thesunRider/ESP32-visual-assistant/Docs/Images/dev.png

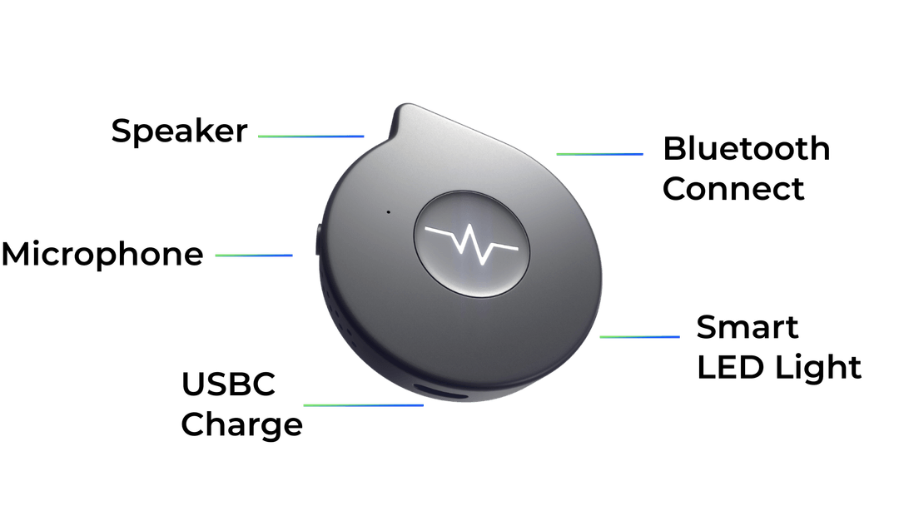
Docs/Images/dev.png
