thesunRider/ESP32-visual-assistant/Docs/Images/wareit.jpeg

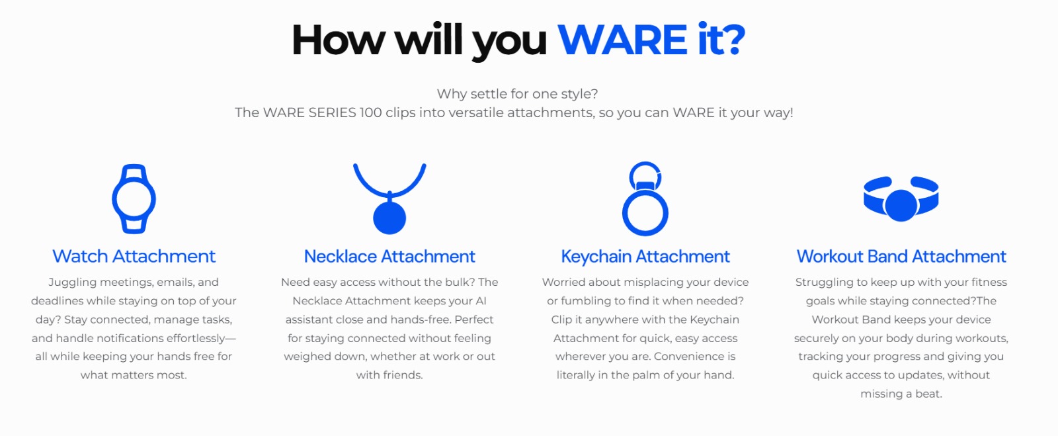
Docs/Images/wareit.jpeg
