thesunRider/ESP32-visual-assistant/Docs/Images/WhatsApp Image 2024-12-23 at 5.31.38 PM.jpeg

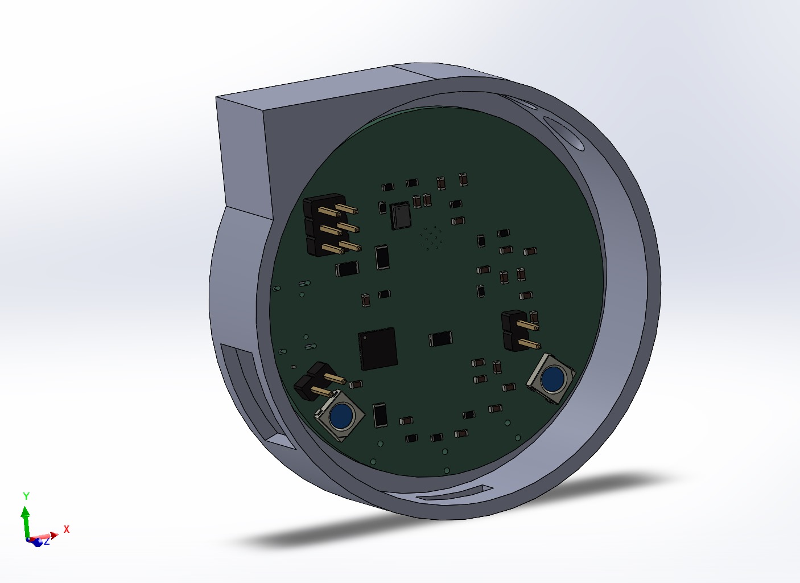
Docs/Images/WhatsApp Image 2024-12-23 at 5.31.38 PM.jpeg
