thesunRider/ESP32-visual-assistant/Docs/Images/WhatsApp Image 2024-12-23 at 6.42.17 PM.jpeg

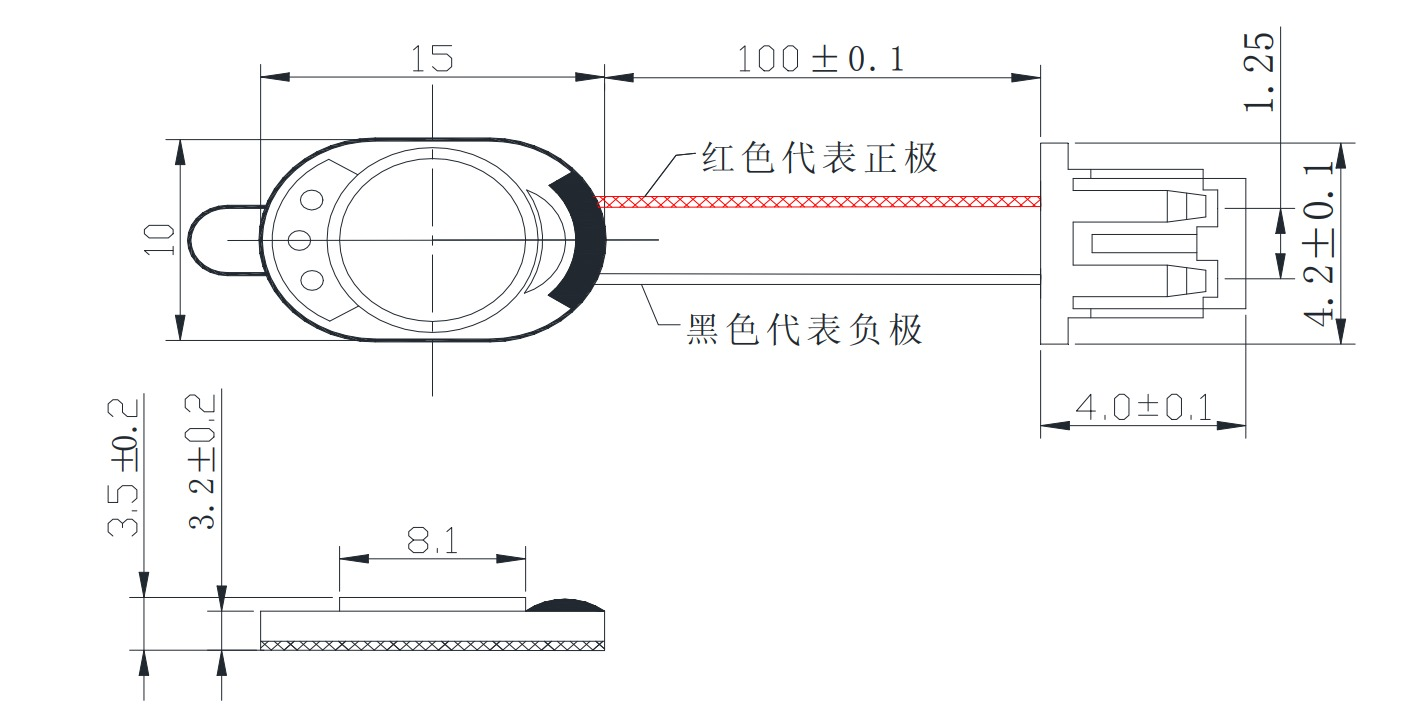
Docs/Images/WhatsApp Image 2024-12-23 at 6.42.17 PM.jpeg
