thesunRider/ESP32-visual-assistant/Docs/Reference Schematic/reference_esp32_amplifier_bff_pcb.jpeg

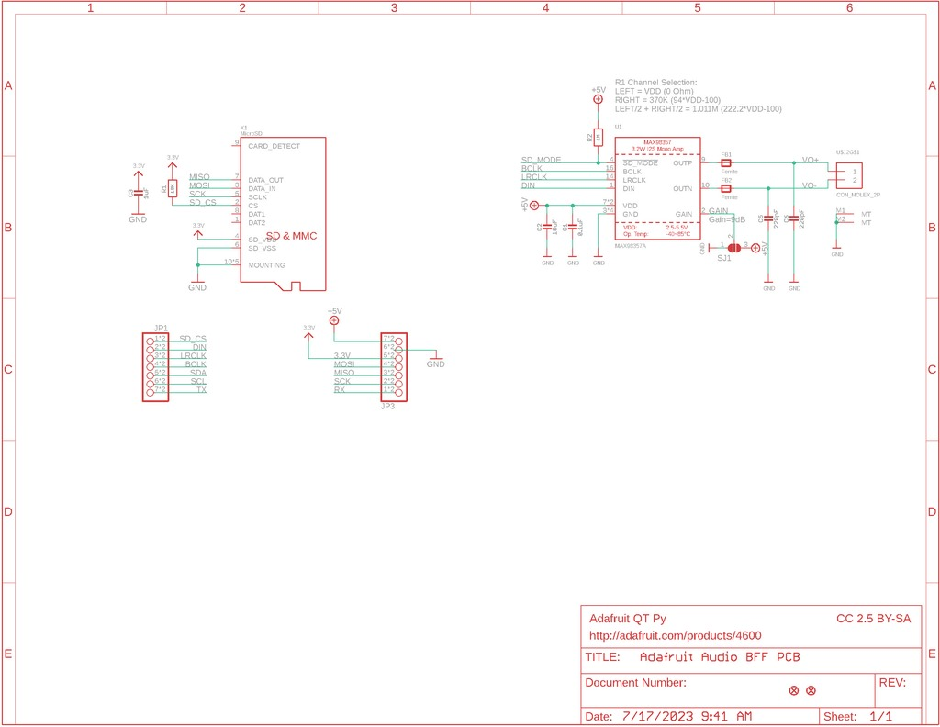
Docs/Reference Schematic/reference_esp32_amplifier_bff_pcb.jpeg
