thesunRider/ESP32-visual-assistant/fllor planning.png

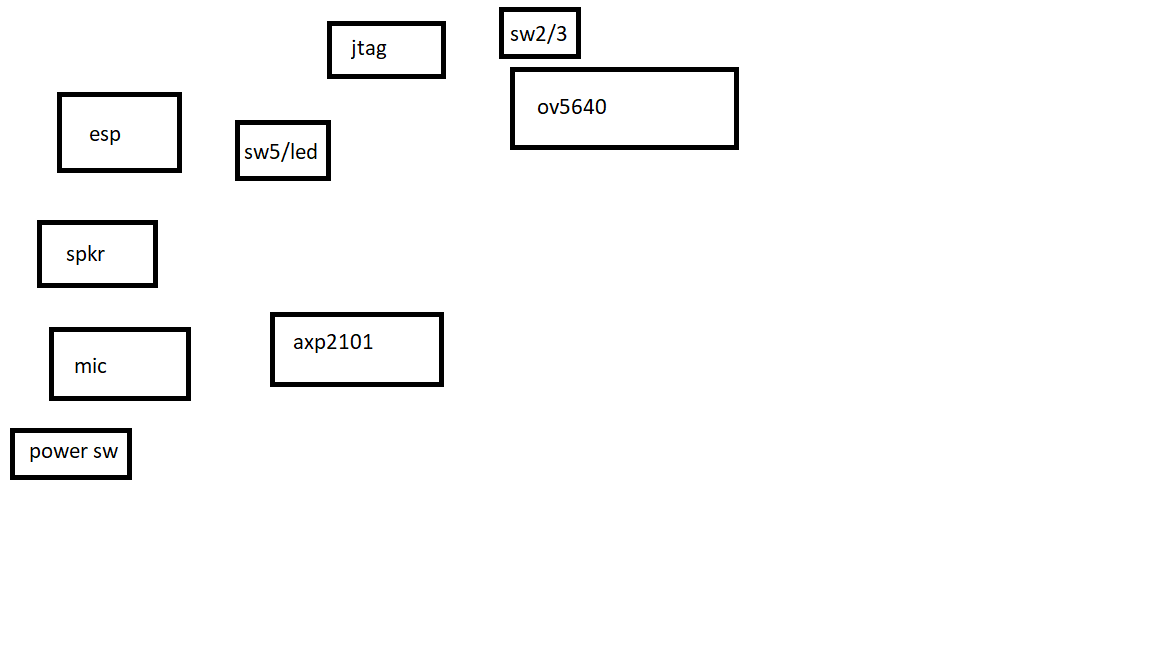
fllor planning.png
