thesunRider/ESP32-visual-assistant/images/case_2.jpg

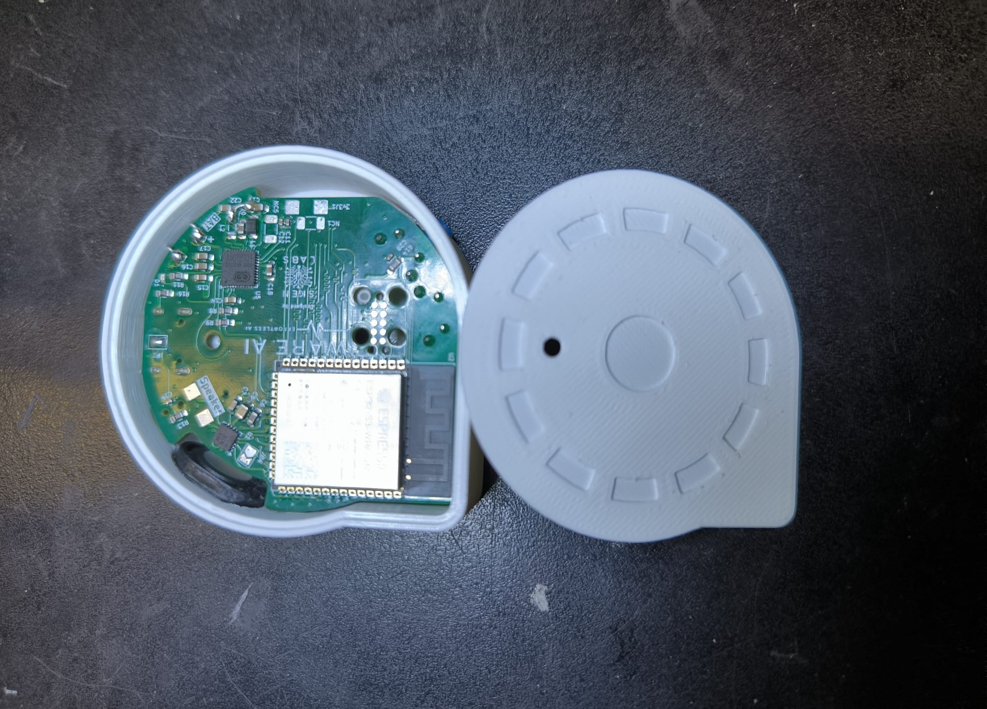
images/case_2.jpg
