thesunRider/ESP32-visual-assistant/images/case_3.jpg

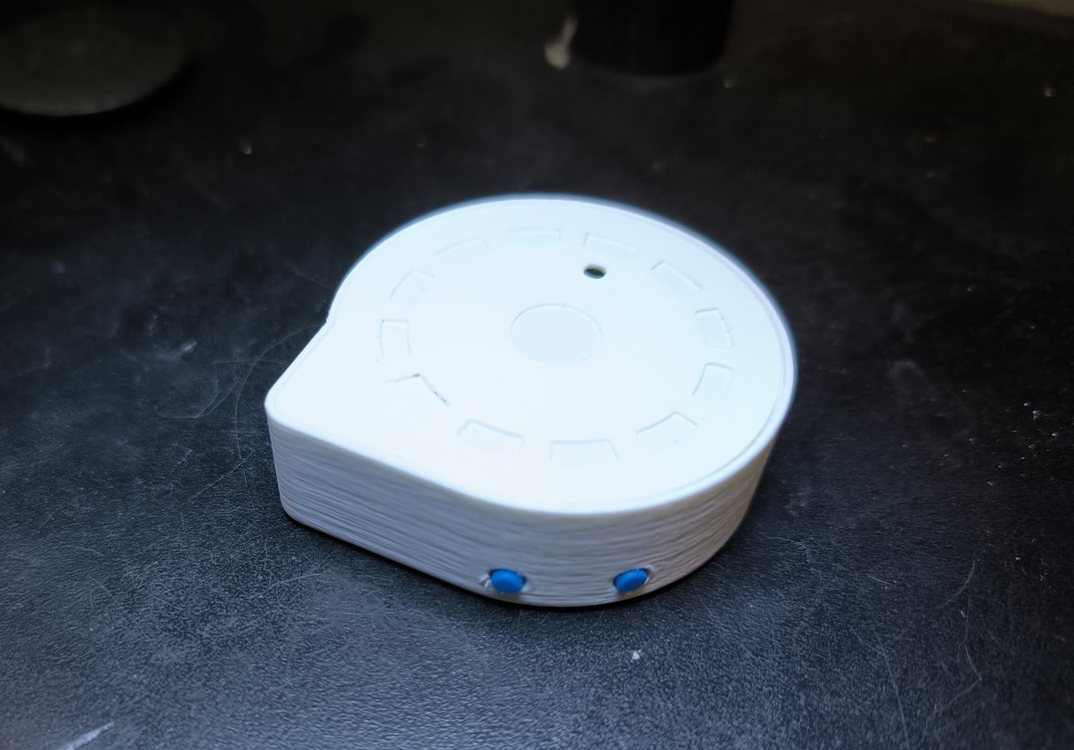
images/case_3.jpg
