thesunRider/ESP32-visual-assistant/images/Microscope_1.jpeg

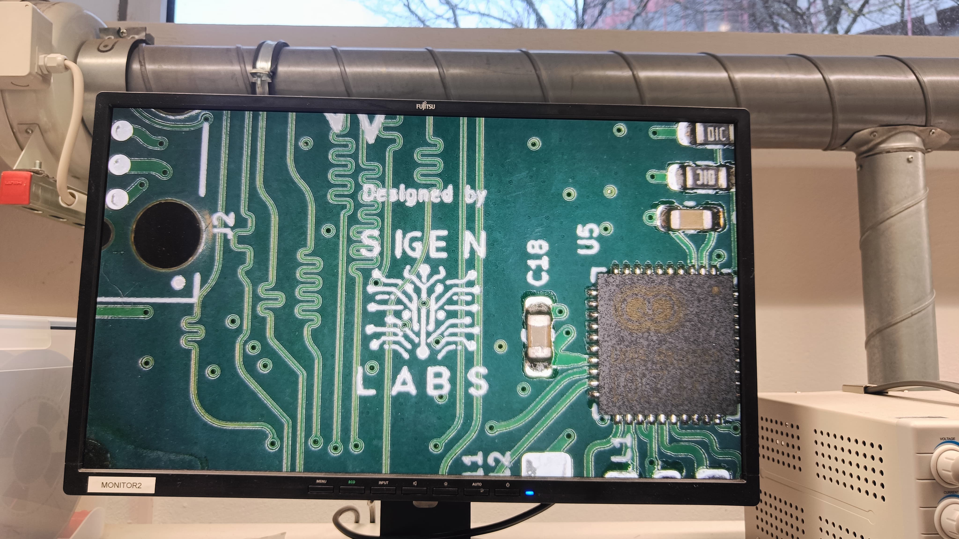
images/Microscope_1.jpeg
