thesunRider/ESP32-visual-assistant/images/PCB_2.jpeg

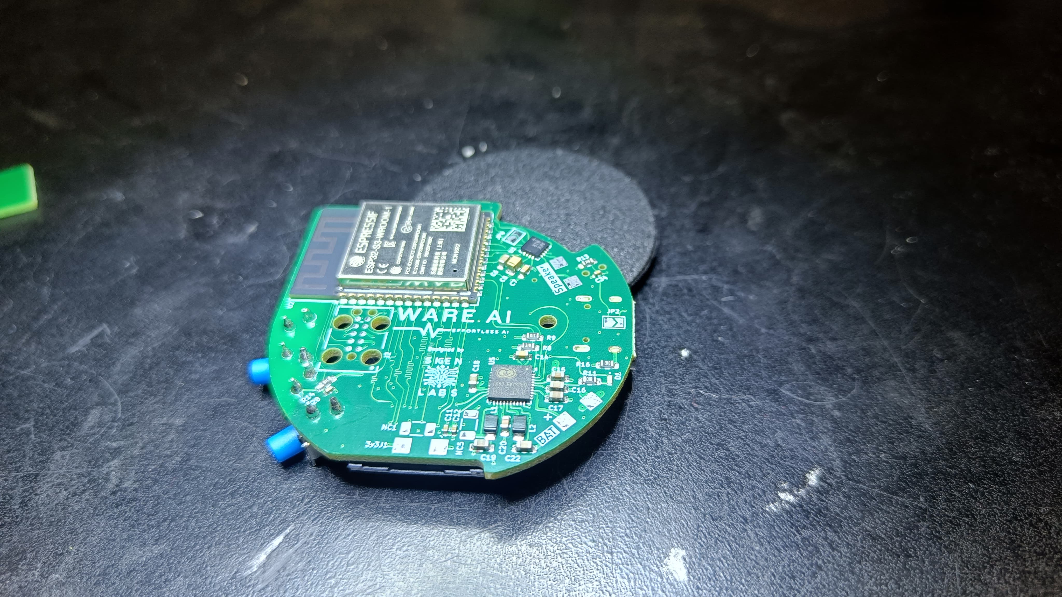
images/PCB_2.jpeg
