thesunRider/ESP32-visual-assistant/images/PCB_Bottom.jpg

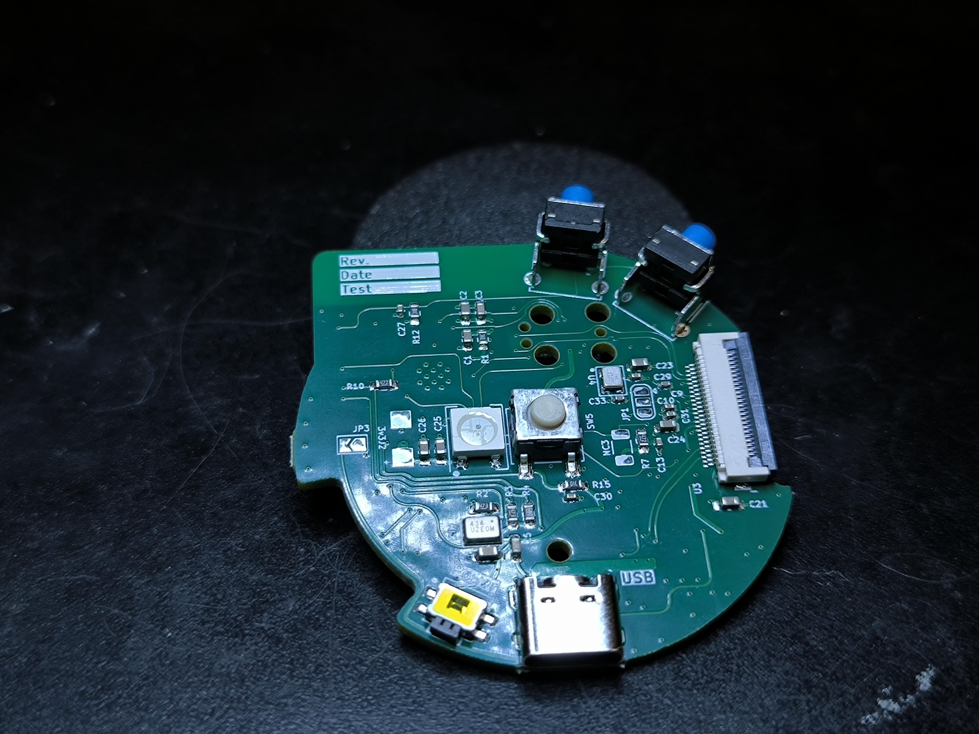
images/PCB_Bottom.jpg
