thesunRider/ESP32-visual-assistant/images/PCB_Top.jpg

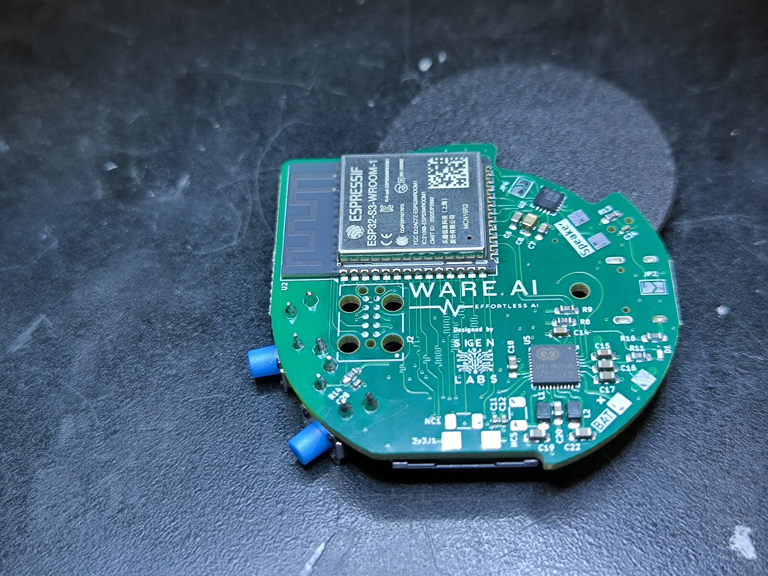
images/PCB_Top.jpg
