thesunRider/ESP32-visual-assistant/Programmer Connection.jpg

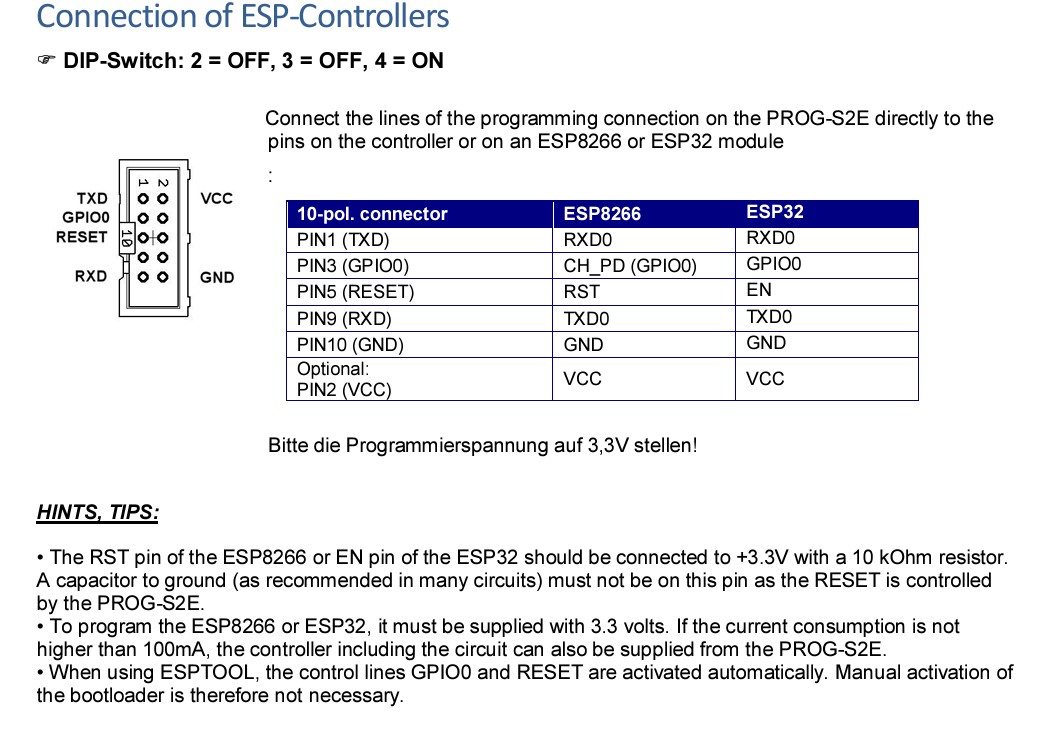
Programmer Connection.jpg
