thesunRider/ESP32-visual-assistant/Model/schematic_rev1.pdf

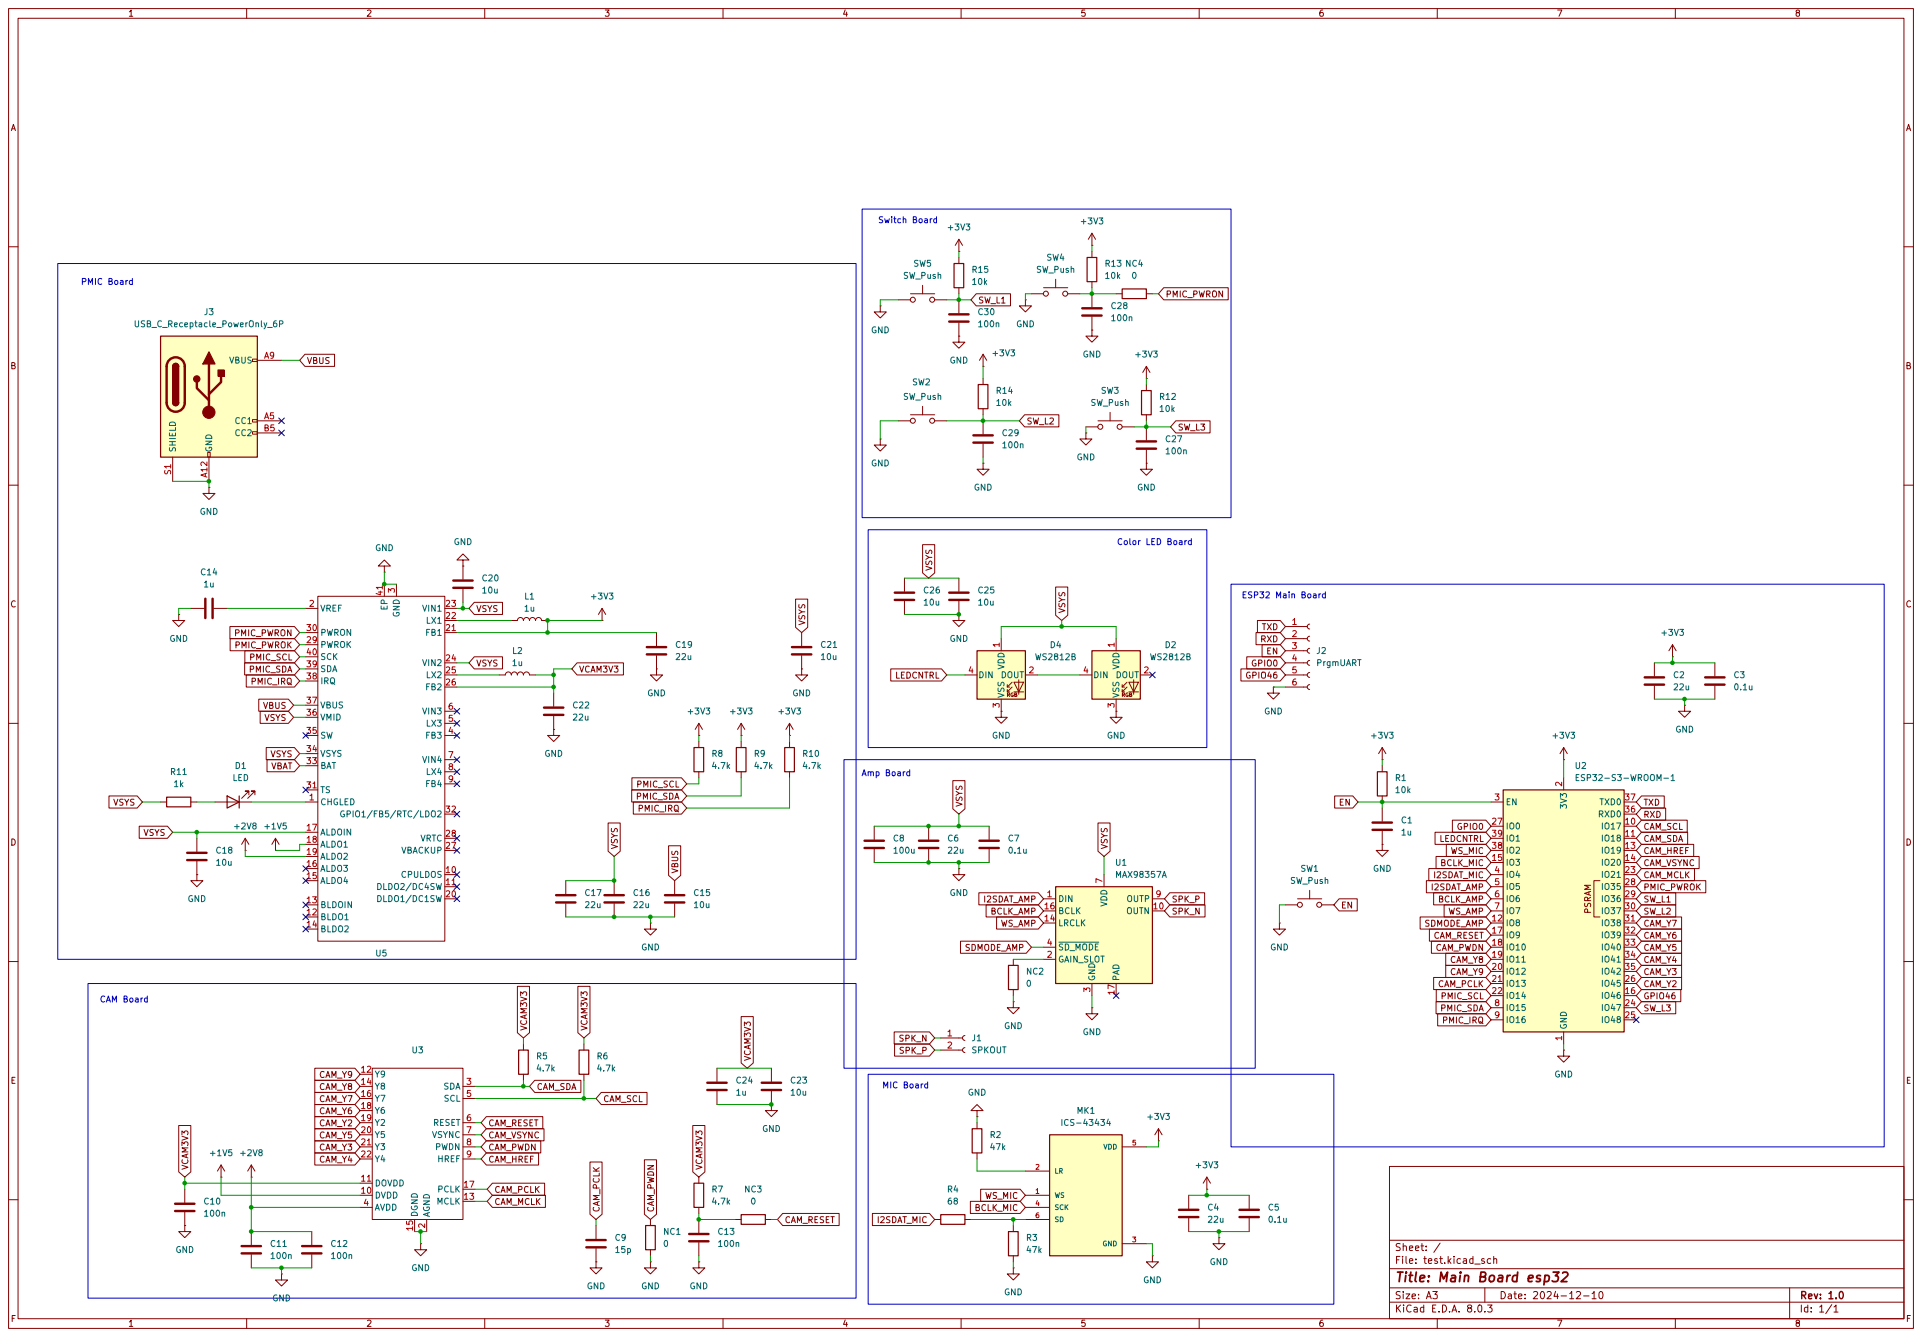
[picture p42: page 1]
