thesunRider/ESP32-visual-assistant/Extras/OV5640-Camera-Board-(A)-Code/OV5640_F746I-C (4.3 inch)/Src/main.c

/**
  ******************************************************************************
  * File Name          : main.c
  * Description        : Main program body
  ******************************************************************************
  ** This notice applies to any and all portions of this file
  * that are not between comment pairs USER CODE BEGIN and
  * USER CODE END. Other portions of this file, whether 
  * inserted by the user or by software development tools
  * are owned by their respective copyright owners.
  *
  * COPYRIGHT(c) 2017 STMicroelectronics
  *
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
  ******************************************************************************
  */

/* Includes ------------------------------------------------------------------*/
#include "main.h"
#include "stm32f7xx_hal.h"
#include "dcmi.h"
#include "dma.h"
#include "dma2d.h"
#include "ltdc.h"
#include "usart.h"
#include "gpio.h"
#include "fmc.h"

/* USER CODE BEGIN Includes */

#include "../BSP/stm32746g_sdram.h"
#include "../BSP/stm32746g_LCD.h"
#include "../BSP/ov5640.h"

/* USER CODE END Includes */


/* USER CODE BEGIN PV */

/* USER CODE END PV */

void SystemClock_Config(void);

/* USER CODE BEGIN PFP */

/* USER CODE END PFP */

int main(void)
{

  /* Enable I-Cache-------------------------------------------------------------*/
  SCB_EnableICache();

  /* Enable D-Cache-------------------------------------------------------------*/
  SCB_EnableDCache();

  /* MCU Configuration----------------------------------------------------------*/

  /* Reset of all peripherals, Initializes the Flash interface and the Systick. */
  HAL_Init();

  /* Configure the system clock */
  SystemClock_Config();

  /* Initialize all configured peripherals */
  MX_GPIO_Init();
  MX_DMA_Init();
  MX_DMA2D_Init();
  MX_FMC_Init();
  MX_LTDC_Init();
  MX_USART1_UART_Init();
  MX_DCMI_Init();

  /* USER CODE BEGIN 2 */
  
  
        BSP_SDRAM_Init();                   
        
	BSP_LCD_Init();
        BSP_LCD_SetLayerVisible(1, DISABLE);
        BSP_LCD_SelectLayer(0);
        BSP_LCD_DisplayOn();
     
        // turn ON the LCD backlight
        HAL_GPIO_WritePin(LCD_BACK_LIGHT_GPIO_Port,LCD_BACK_LIGHT_Pin,GPIO_PIN_SET);  
        BSP_LCD_Clear(LCD_COLOR_WHITE);
        BSP_LCD_SetBackColor(LCD_COLOR_WHITE);
        BSP_LCD_SetTextColor(LCD_COLOR_RED);
	BSP_LCD_SetFont(&Font20);    
        
        BSP_LCD_DisplayStringAt(0, 60, (uint8_t *)"Initializing, please wait ...", CENTER_MODE);
        printf("Initializing, please wait ...\r\n");
        
        while(OV5640_Init())
        {            
                printf("OV5640 error, please check !\r\n");
                BSP_LCD_Clear(LCD_COLOR_WHITE);
                HAL_Delay(200);
                BSP_LCD_DisplayStringAt(0, 60, (uint8_t *)"OV5640 error, please check !", CENTER_MODE);
                HAL_Delay(300);
        }              
        OV5640_RGB565_Mode();	
	OV5640_Light_Mode(0);	   //set auto
	OV5640_Color_Saturation(3); //default
	OV5640_Brightness(4);	//default
	OV5640_Contrast(3);     //default
	OV5640_Sharpness(33);	//set auto
        
        BSP_LCD_Clear(LCD_COLOR_WHITE);
        BSP_LCD_SetTextColor(LCD_COLOR_BLUE);  
        BSP_LCD_DisplayStringAt(0, 60, (uint8_t *)"Waveshare OV5640 Test", CENTER_MODE);
        BSP_LCD_DisplayStringAt(0, 130, (uint8_t *)" WAKE UP:   JPEG", LEFT_MODE);
        BSP_LCD_DisplayStringAt(0, 160, (uint8_t *)" JOYSTICK:  RGB565", LEFT_MODE);
        
        printf("Waveshare OV5640 Test Start !\r\n");
        printf("WAKE UP:   JPEG \r\n");
        printf("JOYSTICK:   RGB565 \r\n");       
        
      

  /* USER CODE END 2 */

  /* Infinite loop */
  /* USER CODE BEGIN WHILE */
  while (1)
  {
          
        if(WAKE_UP_KEY_PRESS)
        {
                HAL_Delay(15);
                if(WAKE_UP_KEY_PRESS)
                {                
                        __HAL_RCC_LTDC_CLK_DISABLE();
                        
                        jpeg_test(SVGA_800_600);                                        
                }   
                while(WAKE_UP_KEY_PRESS);   // wait until key restore
        }
        
        if(JOYSTICK_KEY_PRESS)
        {
                HAL_Delay(15);
                if(JOYSTICK_KEY_PRESS)
                {                                                    
                        rgb565_test();                                                                                                       
                }   
                while(JOYSTICK_KEY_PRESS);   // wait until key restore
        }
          
          
  /* USER CODE END WHILE */

  /* USER CODE BEGIN 3 */

  }
  /* USER CODE END 3 */

}

/** System Clock Configuration
*/
void SystemClock_Config(void)
{

  RCC_OscInitTypeDef RCC_OscInitStruct;
  RCC_ClkInitTypeDef RCC_ClkInitStruct;
  RCC_PeriphCLKInitTypeDef PeriphClkInitStruct;

    /**Configure the main internal regulator output voltage 
    */
  __HAL_RCC_PWR_CLK_ENABLE();

  __HAL_PWR_VOLTAGESCALING_CONFIG(PWR_REGULATOR_VOLTAGE_SCALE1);

    /**Initializes the CPU, AHB and APB busses clocks 
    */
  RCC_OscInitStruct.OscillatorType = RCC_OSCILLATORTYPE_HSE;
  RCC_OscInitStruct.HSEState = RCC_HSE_ON;
  RCC_OscInitStruct.PLL.PLLState = RCC_PLL_ON;
  RCC_OscInitStruct.PLL.PLLSource = RCC_PLLSOURCE_HSE;
  RCC_OscInitStruct.PLL.PLLM = 4;
  RCC_OscInitStruct.PLL.PLLN = 216;
  RCC_OscInitStruct.PLL.PLLP = RCC_PLLP_DIV2;
  RCC_OscInitStruct.PLL.PLLQ = 2;
  if (HAL_RCC_OscConfig(&RCC_OscInitStruct) != HAL_OK)
  {
    _Error_Handler(__FILE__, __LINE__);
  }

    /**Activate the Over-Drive mode 
    */
  if (HAL_PWREx_EnableOverDrive() != HAL_OK)
  {
    _Error_Handler(__FILE__, __LINE__);
  }

    /**Initializes the CPU, AHB and APB busses clocks 
    */
  RCC_ClkInitStruct.ClockType = RCC_CLOCKTYPE_HCLK|RCC_CLOCKTYPE_SYSCLK
                              |RCC_CLOCKTYPE_PCLK1|RCC_CLOCKTYPE_PCLK2;
  RCC_ClkInitStruct.SYSCLKSource = RCC_SYSCLKSOURCE_PLLCLK;
  RCC_ClkInitStruct.AHBCLKDivider = RCC_SYSCLK_DIV1;
  RCC_ClkInitStruct.APB1CLKDivider = RCC_HCLK_DIV4;
  RCC_ClkInitStruct.APB2CLKDivider = RCC_HCLK_DIV2;

  if (HAL_RCC_ClockConfig(&RCC_ClkInitStruct, FLASH_LATENCY_7) != HAL_OK)
  {
    _Error_Handler(__FILE__, __LINE__);
  }

  PeriphClkInitStruct.PeriphClockSelection = RCC_PERIPHCLK_LTDC|RCC_PERIPHCLK_USART1;
  PeriphClkInitStruct.PLLSAI.PLLSAIN = 84;
  PeriphClkInitStruct.PLLSAI.PLLSAIR = 3;
  PeriphClkInitStruct.PLLSAI.PLLSAIQ = 2;
  PeriphClkInitStruct.PLLSAI.PLLSAIP = RCC_PLLSAIP_DIV2;
  PeriphClkInitStruct.PLLSAIDivQ = 1;
  PeriphClkInitStruct.PLLSAIDivR = RCC_PLLSAIDIVR_4;
  PeriphClkInitStruct.Usart1ClockSelection = RCC_USART1CLKSOURCE_PCLK2;
  if (HAL_RCCEx_PeriphCLKConfig(&PeriphClkInitStruct) != HAL_OK)
  {
    _Error_Handler(__FILE__, __LINE__);
  }

  HAL_RCC_MCOConfig(RCC_MCO1, RCC_MCO1SOURCE_HSE, RCC_MCODIV_1);

    /**Configure the Systick interrupt time 
    */
  HAL_SYSTICK_Config(HAL_RCC_GetHCLKFreq()/1000);

    /**Configure the Systick 
    */
  HAL_SYSTICK_CLKSourceConfig(SYSTICK_CLKSOURCE_HCLK);

  /* SysTick_IRQn interrupt configuration */
  HAL_NVIC_SetPriority(SysTick_IRQn, 0, 0);
}

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
