thesunRider/ESP32-visual-assistant/Extras/OV5640-Camera-Board-(A)-Code/OV5640_F429I-C/BSP/stm324x9i_sdram.c

/**
  ******************************************************************************
  * @file    stm324x9i_eval_sdram.c
  * @author  MCD Application Team
  * @version V2.2.1
  * @date    07-October-2015
  * @brief   This file includes the SDRAM driver for the MT48LC4M32B2B5-7 memory 
  *          device mounted on STM324x9I-EVAL evaluation board.
  ******************************************************************************
  * @attention
  *
  * <h2><center>&copy; COPYRIGHT(c) 2015 STMicroelectronics</center></h2>
  *
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
  ******************************************************************************
  */

/* File Info : -----------------------------------------------------------------
                                   User NOTES
1. How To use this driver:
--------------------------
   - This driver is used to drive the MT48LC4M32B2B5-7 SDRAM external memory mounted
     on STM324x9I-EVAL evaluation board.
   - This driver does not need a specific component driver for the SDRAM device
     to be included with.

2. Driver description:
---------------------
  + Initialization steps:
     o Initialize the SDRAM external memory using the BSP_SDRAM_Init() function. This 
       function includes the MSP layer hardware resources initialization and the
       FMC controller configuration to interface with the external SDRAM memory.
     o It contains the SDRAM initialization sequence to program the SDRAM external 
       device using the function BSP_SDRAM_Initialization_sequence(). Note that this 
       sequence is standard for all SDRAM devices, but can include some differences
       from a device to another. If it is the case, the right sequence should be 
       implemented separately.
  
  + SDRAM read/write operations
     o SDRAM external memory can be accessed with read/write operations once it is
       initialized.
       Read/write operation can be performed with AHB access using the functions
       BSP_SDRAM_ReadData()/BSP_SDRAM_WriteData(), or by DMA transfer using the functions
       BSP_SDRAM_ReadData_DMA()/BSP_SDRAM_WriteData_DMA().
     o The AHB access is performed with 32-bit width transaction, the DMA transfer
       configuration is fixed at single (no burst) word transfer (see the 
       SDRAM_MspInit() static function).
     o User can implement his own functions for read/write access with his desired 
       configurations.
     o If interrupt mode is used for DMA transfer, the function BSP_SDRAM_DMA_IRQHandler()
       is called in IRQ handler file, to serve the generated interrupt once the DMA 
       transfer is complete.
     o You can send a command to the SDRAM device in runtime using the function 
       BSP_SDRAM_Sendcmd(), and giving the desired command as parameter chosen between 
       the predefined commands of the "FMC_SDRAM_CommandTypeDef" structure. 
 
------------------------------------------------------------------------------*/

/* Includes ------------------------------------------------------------------*/
#include "stm324x9i_sdram.h"
#include "fmc.h"
/** @addtogroup BSP
  * @{
  */

/** @addtogroup STM324x9I_EVAL
  * @{
  */ 
  
/** @defgroup STM324x9I_EVAL_SDRAM
  * @{
  */ 

/** @defgroup STM324x9I_EVAL_SDRAM_Private_Types_Definitions
  * @{
  */ 
/**
  * @}
  */

/** @defgroup STM324x9I_EVAL_SDRAM_Private_Defines
  * @{
  */
/**
  * @}
  */

/** @defgroup STM324x9I_EVAL_SDRAM_Private_Macros
  * @{
  */  
/**
  * @}
  */

/** @defgroup STM324x9I_EVAL_SDRAM_Private_Variables
  * @{
  */       
static FMC_SDRAM_CommandTypeDef Command;
/**
  * @}
  */ 

/** @defgroup STM324x9I_EVAL_SDRAM_Private_Function_Prototypes
  * @{
  */ 

/**
  * @}
  */
    
/** @defgroup STM324x9I_EVAL_SDRAM_Private_Functions
  * @{
  */ 

/**
  * @brief  Initializes the SDRAM device.
  * @param  None
  * @retval SDRAM status
  */
uint8_t BSP_SDRAM_Init(void)
{ 
  static uint8_t sdramstatus = SDRAM_ERROR;

  /* SDRAM initialization sequence */
  BSP_SDRAM_Initialization_sequence(REFRESH_COUNT);
  
  return sdramstatus;
}

/**
  * @brief  Programs the SDRAM device.
  * @param  RefreshCount: SDRAM refresh counter value 
  * @retval None
  */
void BSP_SDRAM_Initialization_sequence(uint32_t RefreshCount)
{
  __IO uint32_t tmpmrd = 0;
  
  /* Step 1: Configure a clock configuration enable command */
  Command.CommandMode            = FMC_SDRAM_CMD_CLK_ENABLE;
  Command.CommandTarget          = FMC_SDRAM_CMD_TARGET_BANK2;
  Command.AutoRefreshNumber      = 1;
  Command.ModeRegisterDefinition = 0;

  /* Send the command */
  HAL_SDRAM_SendCommand(&hsdram1, &Command, SDRAM_TIMEOUT);

  /* Step 2: Insert 100 us minimum delay */ 
  /* Inserted delay is equal to 1 ms due to systick time base unit (ms) */
  HAL_Delay(1);
    
  /* Step 3: Configure a PALL (precharge all) command */ 
  Command.CommandMode            = FMC_SDRAM_CMD_PALL;
  Command.CommandTarget          = FMC_SDRAM_CMD_TARGET_BANK2;
  Command.AutoRefreshNumber      = 1;
  Command.ModeRegisterDefinition = 0;

  /* Send the command */
  HAL_SDRAM_SendCommand(&hsdram1, &Command, SDRAM_TIMEOUT);  
  
  /* Step 4: Configure an Auto Refresh command */ 
  Command.CommandMode            = FMC_SDRAM_CMD_AUTOREFRESH_MODE;
  Command.CommandTarget          = FMC_SDRAM_CMD_TARGET_BANK2;
  Command.AutoRefreshNumber      = 8;
  Command.ModeRegisterDefinition = 0;

  /* Send the command */
  HAL_SDRAM_SendCommand(&hsdram1, &Command, SDRAM_TIMEOUT);
  
  /* Step 5: Program the external memory mode register */
  tmpmrd = (uint32_t)SDRAM_MODEREG_BURST_LENGTH_1          |\
                     SDRAM_MODEREG_BURST_TYPE_SEQUENTIAL   |\
                     SDRAM_MODEREG_CAS_LATENCY_3           |\
                     SDRAM_MODEREG_OPERATING_MODE_STANDARD |\
                     SDRAM_MODEREG_WRITEBURST_MODE_SINGLE;
  
  Command.CommandMode            = FMC_SDRAM_CMD_LOAD_MODE;
  Command.CommandTarget          = FMC_SDRAM_CMD_TARGET_BANK2;
  Command.AutoRefreshNumber      = 1;
  Command.ModeRegisterDefinition = tmpmrd;

  /* Send the command */
  HAL_SDRAM_SendCommand(&hsdram1, &Command, SDRAM_TIMEOUT);
  
  /* Step 6: Set the refresh rate counter */
  /* Set the device refresh rate */
  HAL_SDRAM_ProgramRefreshRate(&hsdram1, RefreshCount); 
}

/**
  * @brief  Reads an mount of data from the SDRAM memory in polling mode. 
  * @param  uwStartAddress: Read start address
  * @param  pData: Pointer to data to be read  
  * @param  uwDataSize: Size of read data from the memory
  * @retval SDRAM status
  */
uint8_t BSP_SDRAM_ReadData(uint32_t uwStartAddress, uint32_t *pData, uint32_t uwDataSize)
{
  if(HAL_SDRAM_Read_32b(&hsdram1, (uint32_t *)uwStartAddress, pData, uwDataSize) != HAL_OK)
  {
    return SDRAM_ERROR;
  }
  else
  {
    return SDRAM_OK;
  } 
}

/**
  * @brief  Reads an mount of data from the SDRAM memory in DMA mode. 
  * @param  uwStartAddress: Read start address
  * @param  pData: Pointer to data to be read  
  * @param  uwDataSize: Size of read data from the memory
  * @retval SDRAM status
  */
uint8_t BSP_SDRAM_ReadData_DMA(uint32_t uwStartAddress, uint32_t *pData, uint32_t uwDataSize)
{
  if(HAL_SDRAM_Read_DMA(&hsdram1, (uint32_t *)uwStartAddress, pData, uwDataSize) != HAL_OK)
  {
    return SDRAM_ERROR;
  }
  else
  {
    return SDRAM_OK;
  }     
}

/**
  * @brief  Writes an mount of data to the SDRAM memory in polling mode.
  * @param  uwStartAddress: Write start address
  * @param  pData: Pointer to data to be written  
  * @param  uwDataSize: Size of written data from the memory
  * @retval SDRAM status
  */
uint8_t BSP_SDRAM_WriteData(uint32_t uwStartAddress, uint16_t *pData, uint32_t uwDataSize) 
{
  if(HAL_SDRAM_Write_16b(&hsdram1, (uint32_t *)uwStartAddress, pData, uwDataSize) != HAL_OK)
  {
    return SDRAM_ERROR;
  }
  else
  {
    return SDRAM_OK;
  }
}

/**
  * @brief  Writes an mount of data to the SDRAM memory in DMA mode.
  * @param  uwStartAddress: Write start address
  * @param  pData: Pointer to data to be written  
  * @param  uwDataSize: Size of written data from the memory
  * @retval SDRAM status
  */
uint8_t BSP_SDRAM_WriteData_DMA(uint32_t uwStartAddress, uint32_t *pData, uint32_t uwDataSize) 
{
  if(HAL_SDRAM_Write_DMA(&hsdram1, (uint32_t *)uwStartAddress, pData, uwDataSize) != HAL_OK)
  {
    return SDRAM_ERROR;
  }
  else
  {
    return SDRAM_OK;
  } 
}

/**
  * @brief  Sends command to the SDRAM bank.
  * @param  SdramCmd: Pointer to SDRAM command structure 
  * @retval HAL status
  */  
uint8_t BSP_SDRAM_Sendcmd(FMC_SDRAM_CommandTypeDef *SdramCmd)
{
  if(HAL_SDRAM_SendCommand(&hsdram1, SdramCmd, SDRAM_TIMEOUT) != HAL_OK)
  {
    return SDRAM_ERROR;
  }
  else
  {
    return SDRAM_OK;
  }
}

/**
  * @brief  Handles SDRAM DMA transfer interrupt request.
  * @param  None
  * @retval None
  */
void BSP_SDRAM_DMA_IRQHandler(void)
{
  HAL_DMA_IRQHandler(hsdram1.hdma); 
}

/**
  * @brief  Initializes SDRAM MSP.
  * @param  None
  * @retval None
  */

/**
  * @}
  */  
  
/**
  * @}
  */ 
  
/**
  * @}
  */ 
  
/**
  * @}
  */ 

/************************ (C) COPYRIGHT STMicroelectronics *****END OF FILE****/
