thesunRider/ESP32-visual-assistant/Extras/OV5640-Camera-Board-(A)-Code/OV5640_F407V-C/Src/usart.c

/**
  ******************************************************************************
  * File Name          : USART.c
  * Description        : This file provides code for the configuration
  *                      of the USART instances.
  ******************************************************************************
  ** This notice applies to any and all portions of this file
  * that are not between comment pairs USER CODE BEGIN and
  * USER CODE END. Other portions of this file, whether 
  * inserted by the user or by software development tools
  * are owned by their respective copyright owners.
  *
  * COPYRIGHT(c) 2017 STMicroelectronics
  *
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
  ******************************************************************************
  */

/* Includes ------------------------------------------------------------------*/
#include "usart.h"

#include "gpio.h"
#include "dma.h"

UART_HandleTypeDef huart1;
DMA_HandleTypeDef hdma_usart1_rx;
DMA_HandleTypeDef hdma_usart1_tx;

/* USART1 init function */

void MX_USART1_UART_Init(void)
{

  huart1.Instance = USART1;
  huart1.Init.BaudRate = 921600;
  huart1.Init.WordLength = UART_WORDLENGTH_8B;
  huart1.Init.StopBits = UART_STOPBITS_1;
  huart1.Init.Parity = UART_PARITY_NONE;
  huart1.Init.Mode = UART_MODE_TX_RX;
  huart1.Init.HwFlowCtl = UART_HWCONTROL_NONE;
  huart1.Init.OverSampling = UART_OVERSAMPLING_16;
  if (HAL_UART_Init(&huart1) != HAL_OK)
  {
    _Error_Handler(__FILE__, __LINE__);
  }

}

void HAL_UART_MspInit(UART_HandleTypeDef* uartHandle)
{

  GPIO_InitTypeDef GPIO_InitStruct;
  if(uartHandle->Instance==USART1)
  {
    /* USART1 clock enable */
    __HAL_RCC_USART1_CLK_ENABLE();
  
    /**USART1 GPIO Configuration    
    PA9     ------> USART1_TX
    PA10     ------> USART1_RX 
    */
    GPIO_InitStruct.Pin = GPIO_PIN_9|GPIO_PIN_10;
    GPIO_InitStruct.Mode = GPIO_MODE_AF_PP;
    GPIO_InitStruct.Pull = GPIO_PULLUP;
    GPIO_InitStruct.Speed = GPIO_SPEED_FREQ_VERY_HIGH;
    GPIO_InitStruct.Alternate = GPIO_AF7_USART1;
    HAL_GPIO_Init(GPIOA, &GPIO_InitStruct);

    /* USART1 DMA Init */
    /* USART1_RX Init */
    hdma_usart1_rx.Instance = DMA2_Stream2;
    hdma_usart1_rx.Init.Channel = DMA_CHANNEL_4;
    hdma_usart1_rx.Init.Direction = DMA_PERIPH_TO_MEMORY;
    hdma_usart1_rx.Init.PeriphInc = DMA_PINC_DISABLE;
    hdma_usart1_rx.Init.MemInc = DMA_MINC_ENABLE;
    hdma_usart1_rx.Init.PeriphDataAlignment = DMA_PDATAALIGN_BYTE;
    hdma_usart1_rx.Init.MemDataAlignment = DMA_MDATAALIGN_BYTE;
    hdma_usart1_rx.Init.Mode = DMA_NORMAL;
    hdma_usart1_rx.Init.Priority = DMA_PRIORITY_LOW;
    hdma_usart1_rx.Init.FIFOMode = DMA_FIFOMODE_DISABLE;
    if (HAL_DMA_Init(&hdma_usart1_rx) != HAL_OK)
    {
      _Error_Handler(__FILE__, __LINE__);
    }

    __HAL_LINKDMA(uartHandle,hdmarx,hdma_usart1_rx);

    /* USART1_TX Init */
    hdma_usart1_tx.Instance = DMA2_Stream7;
    hdma_usart1_tx.Init.Channel = DMA_CHANNEL_4;
    hdma_usart1_tx.Init.Direction = DMA_MEMORY_TO_PERIPH;
    hdma_usart1_tx.Init.PeriphInc = DMA_PINC_DISABLE;
    hdma_usart1_tx.Init.MemInc = DMA_MINC_ENABLE;
    hdma_usart1_tx.Init.PeriphDataAlignment = DMA_PDATAALIGN_BYTE;
    hdma_usart1_tx.Init.MemDataAlignment = DMA_MDATAALIGN_BYTE;
    hdma_usart1_tx.Init.Mode = DMA_NORMAL;
    hdma_usart1_tx.Init.Priority = DMA_PRIORITY_LOW;
    hdma_usart1_tx.Init.FIFOMode = DMA_FIFOMODE_ENABLE;
    hdma_usart1_tx.Init.FIFOThreshold = DMA_FIFO_THRESHOLD_FULL;
    hdma_usart1_tx.Init.MemBurst = DMA_MBURST_SINGLE;
    hdma_usart1_tx.Init.PeriphBurst = DMA_PBURST_SINGLE;
    if (HAL_DMA_Init(&hdma_usart1_tx) != HAL_OK)
    {
      _Error_Handler(__FILE__, __LINE__);
    }

    __HAL_LINKDMA(uartHandle,hdmatx,hdma_usart1_tx);

    /* USART1 interrupt Init */
    HAL_NVIC_SetPriority(USART1_IRQn, 0, 0);
    HAL_NVIC_EnableIRQ(USART1_IRQn);
  }
}

void HAL_UART_MspDeInit(UART_HandleTypeDef* uartHandle)
{

  if(uartHandle->Instance==USART1)
  {
    /* Peripheral clock disable */
    __HAL_RCC_USART1_CLK_DISABLE();
  
    /**USART1 GPIO Configuration    
    PA9     ------> USART1_TX
    PA10     ------> USART1_RX 
    */
    HAL_GPIO_DeInit(GPIOA, GPIO_PIN_9|GPIO_PIN_10);

    /* USART1 DMA DeInit */
    HAL_DMA_DeInit(uartHandle->hdmarx);
    HAL_DMA_DeInit(uartHandle->hdmatx);

    /* USART1 interrupt Deinit */
    HAL_NVIC_DisableIRQ(USART1_IRQn);
  }
} 

/* USER CODE BEGIN 1 */

#ifdef __GNUC__
  /* With GCC/RAISONANCE, small printf (option LD Linker->Libraries->Small printf
     set to 'Yes') calls __io_putchar() */
  #define PUTCHAR_PROTOTYPE int __io_putchar(int ch)
#else
  #define PUTCHAR_PROTOTYPE int fputc(int ch, FILE *f)
#endif /* __GNUC__ */
/**
  * @brief  Retargets the C library printf function to the USART.
  * @param  None
  * @retval None
  */
PUTCHAR_PROTOTYPE
{
        /* write a character to the uartX and Loop until the end of transmission */
        HAL_UART_Transmit(&huart1, (uint8_t *)&ch, 1, 0xFFFF); 

  return ch;
}

/* USER CODE END 1 */

/**
  * @}
  */

/**
  * @}
  */

/************************ (C) COPYRIGHT STMicroelectronics *****END OF FILE****/
