thesunRider/ESP32-visual-assistant/Extras/OV5640-Camera-Board-(A)-Code/OV5640_F429I-C/BSP/ov5640cfg.h

#ifndef _OV5640CFG_H
#define _OV5640CFG_H
#include "ov5640.h" 


const uint16_t OV5640_jpeg_reg_tbl[][2]=
{
	0x4300, 0x30, // YUV 422, YUYV
	0x501f, 0x00, // YUV 422
	// Input clock = 24Mhz
	0x3035, 0x21, // PLL  
	0x3036, 0x69, // PLL 
	0x3c07, 0x07, // lightmeter 1 threshold[7:0] 
	0x3820, 0x46, // flip
	0x3821, 0x20, // mirror									 
	0x3814, 0x11, // timing X inc 
	0x3815, 0x11, // timing Y inc 
	0x3800, 0x00, // HS 
	0x3801, 0x00, // HS 
	0x3802, 0x00, // VS 
	0x3803, 0x00, // VS 
	0x3804, 0x0a, // HW (HE)		 
	0x3805, 0x3f, // HW (HE)
	0x3806, 0x07, // VH (VE)		 
	0x3807, 0x9f, // VH (VE) 
	
	0x3808, 0x02, // DVPHO 	   
	0x3809, 0x80, // DVPHO 
	0x380a, 0x01, // DVPVO 		
	0x380b, 0xe0, // DVPVO

	0x380c, 0x0b, // HTS 		//
	0x380d, 0x1c, // HTS 
	0x380e, 0x07, // VTS 		//
	0x380f, 0xb0, // VTS 
	0x3813, 0x04, // timing V offset   04
	0x3618, 0x04,
	0x3612, 0x2b,
	0x3709, 0x12,
	0x370c, 0x00, 
        
        0x3a02, 0x02, // 60Hz max exposure
	0x3a03, 0xe0, // 60Hz max exposure 
	0x3a14, 0x02, // 50Hz max exposure
	0x3a15, 0xe0, // 50Hz max exposure        
	
	0x4004, 0x06, // BLC line number 
	0x3002, 0x00, // enable JFIFO, SFIFO, JPG 
	0x3006, 0xff, // enable clock of JPEG2x, JPEG
	0x4713, 0x03, // JPEG mode 3
	0x4407, 0x01, // Quantization sacle 
	0x460b, 0x35,
	0x460c, 0x22,
	0x4837, 0x16, // MIPI global timing 
	0x3824, 0x02, // PCLK manual divider 
	0x5001, 0xA3, // SDE on, Scaling on, CMX on, AWB on 
	0x3503, 0x00, // AEC/AGC on	
};
 
const uint16_t ov5640_init_reg_tbl[][2]= 
{   
	// 24MHz input clock, 24MHz PCLK
	0x3008, 0x42, // software power down, bit[6]
	0x3103, 0x03, // system clock from PLL, bit[1]
	0x3017, 0xff, // FREX, Vsync, HREF, PCLK, D[9:6] output enable
	0x3018, 0xff, // D[5:0], GPIO[1:0] output enable
	0x3034, 0x1a, // MIPI 10-bit
	0x3037, 0x13, // PLL root divider, bit[4], PLL pre-divider, bit[3:0]
	0x3108, 0x01, // PCLK root divider, bit[5:4], SCLK2x root divider, bit[3:2]

	// SCLK root divider, bit[1:0]
	0x3630, 0x36,
	0x3631, 0x0e,
	0x3632, 0xe2,
	0x3633, 0x12,
	0x3621, 0xe0,
	0x3704, 0xa0,
	0x3703, 0x5a,
	0x3715, 0x78,
	0x3717, 0x01,
	0x370b, 0x60,
	0x3705, 0x1a,
	0x3905, 0x02,
	0x3906, 0x10,
	0x3901, 0x0a,
	0x3731, 0x12,
	0x3600, 0x08, // VCM control
	0x3601, 0x33, // VCM control
	0x302d, 0x60, // system control
	0x3620, 0x52,
	0x371b, 0x20,
	0x471c, 0x50,
	0x3a13, 0x43, // pre-gain = 1.047x
	0x3a18, 0x00, // gain ceiling
	0x3a19, 0xf8, // gain ceiling = 15.5x
	0x3635, 0x13,
	0x3636, 0x03,
	0x3634, 0x40,
	0x3622, 0x01,
	// 50/60Hz detection 50/60Hz 
	0x3c01, 0x34, // Band auto, bit[7]
	0x3c04, 0x28, // threshold low sum
	0x3c05, 0x98, // threshold high sum
	0x3c06, 0x00, // light meter 1 threshold[15:8]
	0x3c07, 0x08, // light meter 1 threshold[7:0]
	0x3c08, 0x00, // light meter 2 threshold[15:8]
	0x3c09, 0x1c, // light meter 2 threshold[7:0]
	0x3c0a, 0x9c, // sample number[15:8]
	0x3c0b, 0x40, // sample number[7:0]
	0x3810, 0x00, // Timing Hoffset[11:8]
	0x3811, 0x10, // Timing Hoffset[7:0]
	0x3812, 0x00, // Timing Voffset[10:8]
	0x3708, 0x64,
	0x4001, 0x02, // BLC start from line 2
	0x4005, 0x1a, // BLC always update
	0x3000, 0x00, // enable blocks
	0x3004, 0xff, // enable clocks
	0x300e, 0x58, // MIPI power down, DVP enable
	0x302e, 0x00,
	0x4300, 0x30, // YUV 422, YUYV
	0x501f, 0x00, // YUV 422
	0x440e, 0x00,
	0x5000, 0xa7, // Lenc on, raw gamma on, BPC on, WPC on, CIP on
	// AEC target 
	0x3a0f, 0x30, // stable range in high
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
	0x5309, 0x08, // CIP sharpen TH threshold 1
	0x530a, 0x30, // CIP sharpen TH threshold 2
	0x530b, 0x04, // CIP sharpen TH offset 1
	0x530c, 0x06, // CIP sharpen TH offset 2
	0x5025, 0x00, 
	0x3008, 0x02, // wake up from standby, bit[6]
	
	0x4740, 0X21, //VSYNC active HIGH
};  

#endif
