thesunRider/ESP32-visual-assistant/Extras/OV5640-Camera-Board-(A)-Code/OV5640_F407V-C/MY_BSP/ov5640.h

#ifndef _OV5640_H
#define _OV5640_H

#include "stm32f4xx.h"


 
#define  OV5640_PWDN_Pin_RESET   HAL_GPIO_WritePin(OV5640_PWDN_GPIO_Port, OV5640_PWDN_Pin, GPIO_PIN_RESET)


#define OV5640_ID               0X5640  
#define OV5640_ADDR        	0X78		
#define OV5640_CHIPIDH          0X300A  	
#define OV5640_CHIPIDL          0X300B  	

#define   USER_KEY_PRESS        HAL_GPIO_ReadPin(USER_KEY_GPIO_Port, USER_KEY_Pin) == 0
#define   WAKE_UP_KEY_PRESS     HAL_GPIO_ReadPin(WAKE_UP_KEY_GPIO_Port, WAKE_UP_KEY_Pin) == 0

#define   XSIZE      320
#define   YSIZE      240
#define   LCD_GRAM_ADDRESS   0x60020000     // FSMC Bank1 NOR/PSRM 1   (LCD_RS=1)


#define   QQVGA_160_120    0
#define   QCIF_176_144     1
#define   QVGA_320_240     2
#define   WQVGA_400_240    3
#define   CIF_352_288      4

#define   jpeg_buf_size     30*1024	




uint8_t OV5640_WR_Reg(uint16_t reg,uint8_t data);
uint8_t OV5640_RD_Reg(uint16_t reg);
uint8_t OV5640_Init(void);  
void OV5640_JPEG_Mode(void);
void OV5640_RGB565_Mode(void);
void OV5640_Exposure(uint8_t exposure);
void OV5640_Light_Mode(uint8_t mode);
void OV5640_Color_Saturation(uint8_t sat);
void OV5640_Brightness(uint8_t bright);
void OV5640_Contrast(uint8_t contrast);
void OV5640_Sharpness(uint8_t sharp);
void OV5640_Special_Effects(uint8_t eft);
void OV5640_Test_Pattern(uint8_t mode);
void OV5640_Flash_Lamp(uint8_t sw);
uint8_t OV5640_OutSize_Set(uint16_t offx,uint16_t offy,uint16_t width,uint16_t height);
uint8_t OV5640_Focus_Init(void);
uint8_t OV5640_Auto_Focus(void);
void rgb565_test(void);
void jpeg_test(uint8_t jpg_size);

#endif
