thesunRider/ESP32-visual-assistant/Extras/OV5640-Camera-Board-(A)-Code/OV5640_F746I-C (4.3 inch)/BSP/sccb.h

#ifndef __SCCB_H
#define __SCCB_H

#include "stm32f7xx.h"




#define    OV5640_SIOC_H()       HAL_GPIO_WritePin(OV5640_SIOC_GPIO_Port, OV5640_SIOC_Pin, GPIO_PIN_SET)
#define    OV5640_SIOC_L()       HAL_GPIO_WritePin(OV5640_SIOC_GPIO_Port, OV5640_SIOC_Pin, GPIO_PIN_RESET)
#define    OV5640_SIOD_H()       HAL_GPIO_WritePin(OV5640_SIOD_GPIO_Port, OV5640_SIOD_Pin, GPIO_PIN_SET)
#define    OV5640_SIOD_L()       HAL_GPIO_WritePin(OV5640_SIOD_GPIO_Port, OV5640_SIOD_Pin, GPIO_PIN_RESET)

#define    OV5640_SIOD_READ()     HAL_GPIO_ReadPin(OV5640_SIOD_GPIO_Port, OV5640_SIOD_Pin)


void SCCB_Init(void);
void SCCB_Start(void);
void SCCB_Stop(void);
void SCCB_No_Ack(void);
uint8_t SCCB_WR_Byte(uint8_t dat);
uint8_t SCCB_RD_Byte(void);
#endif
